JaredLeslie-Techie/IIoT-Smart-Factory/firmware/ESP8266_Smart_Factory/secrets.example.h

#pragma once

// Copy this file to secrets.h in the same folder and replace these values.
// Keep secrets.h on your computer; the repository .gitignore excludes it.
#define WIFI_SSID "YOUR_WIFI_SSID"
#define WIFI_PASSWORD "YOUR_WIFI_PASSWORD"
#define MQTT_USERNAME "YOUR_MQTT_USERNAME"
#define MQTT_PASSWORD "YOUR_MQTT_PASSWORD"
#define MQTT_SERVER "YOUR_HIVEMQ_BROKER_HOSTNAME.hivemq.cloud"
